electrified/rc2014-mystorm/hdl/src/rc2014_interface_top.v

`default_nettype none

module rc2014_interface_top(
    input [15:0] A,
    input [7:0] D,
    input RD,
    input M1,
    input CLK,
    input MRQ,
    input IORQ,
    input RST,
    input INT,
    input WR,
    output ADDR_DIR,
    output SIG_DIR,
    output DATA_DIR,
    output SIG2_DIR,
    output LED1,
    input BUT1,
    input fpga_clk,
    output uart_tx,
    input BUT2
    );

assign SIG_DIR = 0;
assign SIG2_DIR = 0;
assign DATA_DIR = 1;
assign ADDR_DIR = RD;

reg [31:0] led_countdown = 0;
wire led_track;
 
reg [7:0] request_counter =0;
reg ce = 0;

reg [7:0] romval;

rom blockram(.clk(CLK), 
  .ce(1),
  .addr(A[12:0]), 
  .rdata(romval));

reg debounced_CLK;

debouncer clockdebouncer(
  .CLK(fpga_clk),
  .raw_input(CLK),
  .state(debounced_CLK)
);

reg debounced_RD;

debouncer RDdebouncer(
  .CLK(fpga_clk),
  .raw_input(RD),
  .state(debounced_RD)
);

reg debounced_BUT1;

debouncer BUT1debouncer(
  .CLK(CLK),
  .raw_input(BUT1),
  .state(debounced_BUT1)
);


always @(posedge fpga_clk)
begin
	if (reset) begin
			text[0]  <= "0";
			text[1]  <= "x";
			text[2]  <= "_";
			text[3]  <= "_";
			text[4]  <= "_";
			text[5]  <= "_";
			text[6]  <= " ";
			text[7]  <= "0";
			text[8]  <= "x";
			text[9]  <= "_";
			text[10]  <= "_";
			text[11] <= "\n";
			text[12] <= 'h0d;
			
			text_cntr	<= 0;
			tx_req		<= 1'b0;

			asciidigits[0] <= "s";
			asciidigits[1] <= "c";
			asciidigits[2] <= "r";
			asciidigits[3] <= "w";

		end
		else if (text_cntr == 0) begin
			// asciidigits[0] <= "e";

			text[2]  <= asciidigits[3];
			text[3]  <= asciidigits[2];
			text[4]  <= asciidigits[1];
			text[5]  <= asciidigits[0];

			text[9]  <= asciidigits[5];
			text[10]  <= asciidigits[4];

			tx_req		<= 1'b0;

			if (count == 26'h50000) begin

				case (lastknownaddress[3:0])
					4'h0: asciidigits[0] <= "0";
					4'h1: asciidigits[0] <= "1";
					4'h2: asciidigits[0] <= "2";
					4'h3: asciidigits[0] <= "3";
					4'h4: asciidigits[0] <= "4";
					4'h5: asciidigits[0] <= "5";
					4'h6: asciidigits[0] <= "6";
					4'h7: asciidigits[0] <= "7";
					4'h8: asciidigits[0] <= "8";
					4'h9: asciidigits[0] <= "9";
					4'hA: asciidigits[0] <= "A";
					4'hB: asciidigits[0] <= "B";
					4'hC: asciidigits[0] <= "C";
					4'hD: asciidigits[0] <= "D";
					4'hE: asciidigits[0] <= "E";
					4'hF: asciidigits[0] <= "F";
					default: asciidigits[0] <= "Z";
				endcase

				case (lastknownaddress[7:4])
					4'h0: asciidigits[1] <= "0";
					4'h1: asciidigits[1] <= "1";
					4'h2: asciidigits[1] <= "2";
					4'h3: asciidigits[1] <= "3";
					4'h4: asciidigits[1] <= "4";
					4'h5: asciidigits[1] <= "5";
					4'h6: asciidigits[1] <= "6";
					4'h7: asciidigits[1] <= "7";
					4'h8: asciidigits[1] <= "8";
					4'h9: asciidigits[1] <= "9";
					4'hA: asciidigits[1] <= "A";
					4'hB: asciidigits[1] <= "B";
					4'hC: asciidigits[1] <= "C";
					4'hD: asciidigits[1] <= "D";
					4'hE: asciidigits[1] <= "E";
					4'hF: asciidigits[1] <= "F";
					default: asciidigits[1] <= "Z";
				endcase

				case (lastknownaddress[11:8])
					4'h0: asciidigits[2] <= "0";
					4'h1: asciidigits[2] <= "1";
					4'h2: asciidigits[2] <= "2";
					4'h3: asciidigits[2] <= "3";
					4'h4: asciidigits[2] <= "4";
					4'h5: asciidigits[2] <= "5";
					4'h6: asciidigits[2] <= "6";
					4'h7: asciidigits[2] <= "7";
					4'h8: asciidigits[2] <= "8";
					4'h9: asciidigits[2] <= "9";
					4'hA: asciidigits[2] <= "A";
					4'hB: asciidigits[2] <= "B";
					4'hC: asciidigits[2] <= "C";
					4'hD: asciidigits[2] <= "D";
					4'hE: asciidigits[2] <= "E";
					4'hF: asciidigits[2] <= "F";
					default: asciidigits[2] <= "Z";
				endcase

				case (lastknownaddress[15:12])
					4'h0: asciidigits[3] <= "0";
					4'h1: asciidigits[3] <= "1";
					4'h2: asciidigits[3] <= "2";
					4'h3: asciidigits[3] <= "3";
					4'h4: asciidigits[3] <= "4";
					4'h5: asciidigits[3] <= "5";
					4'h6: asciidigits[3] <= "6";
					4'h7: asciidigits[3] <= "7";
					4'h8: asciidigits[3] <= "8";
					4'h9: asciidigits[3] <= "9";
					4'hA: asciidigits[3] <= "A";
					4'hB: asciidigits[3] <= "B";
					4'hC: asciidigits[3] <= "C";
					4'hD: asciidigits[3] <= "D";
					4'hE: asciidigits[3] <= "E";
					4'hF: asciidigits[3] <= "F";
					default: asciidigits[3] <= "Z";
				endcase


				case (lastknownvalue[3:0])
					4'h0: asciidigits[4] <= "0";
					4'h1: asciidigits[4] <= "1";
					4'h2: asciidigits[4] <= "2";
					4'h3: asciidigits[4] <= "3";
					4'h4: asciidigits[4] <= "4";
					4'h5: asciidigits[4] <= "5";
					4'h6: asciidigits[4] <= "6";
					4'h7: asciidigits[4] <= "7";
					4'h8: asciidigits[4] <= "8";
					4'h9: asciidigits[4] <= "9";
					4'hA: asciidigits[4] <= "A";
					4'hB: asciidigits[4] <= "B";
					4'hC: asciidigits[4] <= "C";
					4'hD: asciidigits[4] <= "D";
					4'hE: asciidigits[4] <= "E";
					4'hF: asciidigits[4] <= "F";
					default: asciidigits[4] <= "Z";
				endcase

				case (lastknownvalue[7:4])
					4'h0: asciidigits[5] <= "0";
					4'h1: asciidigits[5] <= "1";
					4'h2: asciidigits[5] <= "2";
					4'h3: asciidigits[5] <= "3";
					4'h4: asciidigits[5] <= "4";
					4'h5: asciidigits[5] <= "5";
					4'h6: asciidigits[5] <= "6";
					4'h7: asciidigits[5] <= "7";
					4'h8: asciidigits[5] <= "8";
					4'h9: asciidigits[5] <= "9";
					4'hA: asciidigits[5] <= "A";
					4'hB: asciidigits[5] <= "B";
					4'hC: asciidigits[5] <= "C";
					4'hD: asciidigits[5] <= "D";
					4'hE: asciidigits[5] <= "E";
					4'hF: asciidigits[5] <= "F";
					default: asciidigits[5] <= "Z";
				endcase


				tx_req		<= 1'b1;
				tx_data		<= text[text_cntr];
				text_cntr	<= text_cntr + 1;
			end
		end
		else if (tx_ready) begin
			tx_req		<= 1'b1;
			tx_data		<= text[text_cntr];
			text_cntr	<= text_cntr + 1;

			if (text_cntr == 13) begin
				text_cntr	<= 0;
			end
			else begin
				text_cntr	<= text_cntr + 1;
			end
		end

    ce = (A >= 16'h0000 && A < 16'h2000) && !MRQ;
  // if (BUT1 == 1'b0)
  //    begin
        // led_countdown <= 0;
	      // // led_track <= 1'b0;
        led_track <= ~led_track;
    //  end
  end

  assign LED1 = led_track;

  reg [7:0] 	text[0:12];
  reg [16:0]	text_cntr;
  reg [15:0] lastknownaddress = 0;
  reg [7:0] lastknownvalue = 0;
  reg [7:0]	tx_data;
  reg 		tx_req;
  wire		tx_ready;
  wire reset;

  reg [26:0]	count;
  reg [7:0] asciidigits [0:5];
	
  sync_reset u_sync_reset(
		.clk(fpga_clk),
		.reset_in(BUT2),
		.reset_out(reset)
	);

	uart_tx u_uart_tx (
		.clk (fpga_clk),
		.reset (reset),
		.tx_req(tx_req),
		.tx_ready(tx_ready),
		.tx_data(tx_data),
		.uart_tx(uart_tx)
	);

endmodule
