electrified/rc2014-mystorm/hdl/chip.v

// Reading file 'chip.asc'..

module chip (output io_0_16_0, output io_0_16_1, input io_16_33_1, input io_0_27_1, output io_0_11_1, input io_0_28_0, output io_0_11_0, output io_0_18_1, output io_0_17_1, output io_0_17_0, input io_33_29_1, output io_0_20_0, output io_0_20_1, output io_0_18_0, input io_33_31_0, output io_0_22_0, output io_0_22_1, input io_0_27_0, input io_0_25_0, input io_3_33_1, input io_4_33_0, input io_33_30_1, input io_30_33_1, input io_31_33_0, input io_31_33_1, input io_30_33_0, input io_33_30_0, input io_33_27_1, input io_29_0_0, input io_33_23_1, input io_33_20_1, input io_33_21_1, input io_33_28_0, input io_33_21_0, output io_31_0_1);

wire n1;
// (0, 0, 'glb_netwk_0')
// (16, 1, 'sp4_r_v_b_36')
// (16, 2, 'sp4_r_v_b_25')
// (16, 3, 'sp4_r_v_b_12')
// (16, 4, 'sp4_r_v_b_1')
// (16, 5, 'sp4_r_v_b_36')
// (16, 6, 'sp4_r_v_b_25')
// (16, 7, 'sp4_r_v_b_12')
// (16, 8, 'sp4_r_v_b_1')
// (16, 9, 'sp4_r_v_b_36')
// (16, 10, 'neigh_op_tnr_6')
// (16, 10, 'sp4_r_v_b_25')
// (16, 11, 'lutff_global/s_r')
// (16, 11, 'neigh_op_rgt_6')
// (16, 11, 'sp4_r_v_b_12')
// (16, 12, 'lutff_global/s_r')
// (16, 12, 'neigh_op_bnr_6')
// (16, 12, 'sp4_r_v_b_1')
// (17, 0, 'fabout')
// (17, 0, 'local_g1_4')
// (17, 0, 'span4_vert_36')
// (17, 1, 'sp4_v_b_36')
// (17, 2, 'sp4_v_b_25')
// (17, 3, 'sp4_v_b_12')
// (17, 4, 'sp4_v_b_1')
// (17, 4, 'sp4_v_t_36')
// (17, 5, 'sp4_v_b_36')
// (17, 6, 'sp4_v_b_25')
// (17, 7, 'sp4_v_b_12')
// (17, 8, 'sp4_v_b_1')
// (17, 8, 'sp4_v_t_36')
// (17, 9, 'sp4_v_b_36')
// (17, 10, 'neigh_op_top_6')
// (17, 10, 'sp4_v_b_25')
// (17, 11, 'lutff_6/out')
// (17, 11, 'lutff_global/s_r')
// (17, 11, 'sp4_v_b_12')
// (17, 12, 'local_g1_6')
// (17, 12, 'lutff_3/in_2')
// (17, 12, 'neigh_op_bot_6')
// (17, 12, 'sp4_v_b_1')
// (18, 10, 'local_g2_6')
// (18, 10, 'lutff_7/in_1')
// (18, 10, 'lutff_global/s_r')
// (18, 10, 'neigh_op_tnl_6')
// (18, 11, 'neigh_op_lft_6')
// (18, 12, 'neigh_op_bnl_6')

wire io_0_16_0;
assign io_0_16_1 = io_0_16_0;
// (0, 0, 'glb_netwk_3')
// (0, 16, 'io_0/D_OUT_0')
// (0, 16, 'io_0/PAD')
// (0, 16, 'io_1/D_OUT_0')
// (0, 16, 'io_1/PAD')
// (0, 16, 'local_g0_7')
// (0, 16, 'local_g1_7')
// (0, 16, 'span4_horz_7')
// (0, 16, 'span4_vert_t_13')
// (0, 17, 'fabout')
// (0, 17, 'local_g0_5')
// (0, 17, 'span4_vert_b_13')
// (0, 18, 'span4_vert_b_9')
// (0, 19, 'span4_vert_b_5')
// (0, 20, 'span4_horz_7')
// (0, 20, 'span4_vert_b_1')
// (1, 16, 'sp4_h_r_18')
// (1, 20, 'sp4_h_r_18')
// (2, 16, 'sp4_h_r_31')
// (2, 20, 'sp4_h_r_31')
// (3, 16, 'sp4_h_r_42')
// (3, 20, 'sp4_h_r_42')
// (4, 16, 'sp4_h_l_42')
// (4, 16, 'sp4_h_r_11')
// (4, 20, 'sp4_h_l_42')
// (4, 20, 'sp4_h_r_11')
// (5, 16, 'sp4_h_r_22')
// (5, 20, 'sp4_h_r_22')
// (6, 16, 'sp4_h_r_35')
// (6, 20, 'sp4_h_r_35')
// (7, 16, 'sp4_h_r_46')
// (7, 20, 'sp4_h_r_46')
// (7, 24, 'sp4_r_v_b_43')
// (7, 25, 'sp4_r_v_b_30')
// (7, 25, 'sp4_r_v_b_46')
// (7, 26, 'sp4_r_v_b_19')
// (7, 26, 'sp4_r_v_b_35')
// (7, 27, 'sp4_r_v_b_22')
// (7, 27, 'sp4_r_v_b_6')
// (7, 28, 'sp4_r_v_b_11')
// (8, 11, 'sp12_v_t_23')
// (8, 12, 'sp12_v_b_23')
// (8, 13, 'sp12_v_b_20')
// (8, 14, 'sp12_v_b_19')
// (8, 15, 'sp12_v_b_16')
// (8, 16, 'local_g1_3')
// (8, 16, 'ram/WCLK')
// (8, 16, 'ram/WCLKE')
// (8, 16, 'sp12_v_b_15')
// (8, 16, 'sp4_h_l_46')
// (8, 16, 'sp4_h_r_11')
// (8, 16, 'sp4_r_v_b_43')
// (8, 17, 'sp12_v_b_12')
// (8, 17, 'sp4_r_v_b_30')
// (8, 18, 'local_g3_3')
// (8, 18, 'ram/WCLK')
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
// (26, 26, 'sp4_v_b_19')
// (26, 27, 'sp4_v_b_3')
// (26, 27, 'sp4_v_b_6')
// (26, 27, 'sp4_v_t_43')
// (26, 28, 'sp4_v_b_43')
// (26, 29, 'sp4_v_b_30')
// (26, 30, 'sp4_v_b_19')
// (26, 31, 'sp4_v_b_6')
// (27, 20, 'sp4_h_r_35')
// (27, 23, 'sp4_h_r_19')
// (27, 24, 'sp4_h_r_34')
// (28, 20, 'sp4_h_r_46')
// (28, 23, 'sp4_h_r_30')
// (28, 24, 'sp4_h_r_47')
// (29, 20, 'sp4_h_l_46')
// (29, 23, 'sp4_h_r_43')
// (29, 24, 'sp4_h_l_47')
// (30, 23, 'sp4_h_l_43')

wire io_16_33_1;
// (0, 0, 'glb_netwk_4')
// (15, 15, 'lutff_global/clk')
// (15, 32, 'neigh_op_tnr_2')
// (15, 32, 'neigh_op_tnr_6')
// (16, 13, 'lutff_global/clk')
// (16, 14, 'lutff_global/clk')
// (16, 15, 'lutff_global/clk')
// (16, 32, 'neigh_op_top_2')
// (16, 32, 'neigh_op_top_6')
// (16, 33, 'fabout')
// (16, 33, 'io_1/D_IN_0')
// (16, 33, 'io_1/PAD')
// (16, 33, 'local_g1_2')
// (16, 33, 'span4_horz_r_2')
// (17, 32, 'neigh_op_tnl_2')
// (17, 32, 'neigh_op_tnl_6')
// (17, 33, 'span4_horz_r_6')
// (18, 33, 'span4_horz_r_10')
// (19, 33, 'span4_horz_r_14')
// (20, 33, 'span4_horz_l_14')

reg n4 = 0;
// (0, 0, 'glb_netwk_5')
// (6, 20, 'lutff_global/clk')
// (6, 21, 'lutff_global/clk')
// (7, 19, 'lutff_global/clk')
// (7, 20, 'lutff_global/clk')
// (7, 21, 'lutff_global/clk')
// (7, 22, 'lutff_global/clk')
// (15, 1, 'sp4_r_v_b_9')
// (15, 2, 'sp4_r_v_b_43')
// (15, 3, 'sp4_r_v_b_30')
// (15, 4, 'sp4_r_v_b_19')
// (15, 5, 'sp4_r_v_b_6')
// (15, 6, 'sp4_r_v_b_47')
// (15, 7, 'sp4_r_v_b_34')
// (15, 8, 'sp4_r_v_b_23')
// (15, 9, 'sp4_r_v_b_10')
// (15, 10, 'sp4_r_v_b_47')
// (15, 11, 'sp4_r_v_b_34')
// (15, 12, 'neigh_op_tnr_5')
// (15, 12, 'sp4_r_v_b_23')
// (15, 13, 'neigh_op_rgt_5')
// (15, 13, 'sp4_r_v_b_10')
// (15, 14, 'neigh_op_bnr_5')
// (16, 0, 'fabout')
// (16, 0, 'local_g0_1')
// (16, 0, 'span4_vert_9')
// (16, 1, 'sp4_v_b_9')
// (16, 1, 'sp4_v_t_43')
// (16, 2, 'sp4_v_b_43')
// (16, 3, 'sp4_v_b_30')
// (16, 4, 'sp4_v_b_19')
// (16, 5, 'sp4_v_b_6')
// (16, 5, 'sp4_v_t_47')
// (16, 6, 'sp4_v_b_47')
// (16, 7, 'sp4_v_b_34')
// (16, 8, 'sp4_v_b_23')
// (16, 9, 'sp4_v_b_10')
// (16, 9, 'sp4_v_t_47')
// (16, 10, 'sp4_v_b_47')
// (16, 11, 'lutff_global/clk')
// (16, 11, 'sp4_v_b_34')
// (16, 12, 'lutff_global/clk')
// (16, 12, 'neigh_op_top_5')
// (16, 12, 'sp4_v_b_23')
// (16, 13, 'local_g0_5')
// (16, 13, 'lutff_5/in_0')
// (16, 13, 'lutff_5/out')
// (16, 13, 'sp4_v_b_10')
// (16, 14, 'local_g1_5')
// (16, 14, 'lutff_4/in_0')
// (16, 14, 'neigh_op_bot_5')
// (17, 11, 'lutff_global/clk')
// (17, 12, 'neigh_op_tnl_5')
// (17, 13, 'neigh_op_lft_5')
// (17, 14, 'neigh_op_bnl_5')
// (18, 10, 'lutff_global/clk')

wire io_0_27_1;
// (0, 0, 'glb_netwk_6')
// (0, 15, 'span4_vert_t_14')
// (0, 16, 'fabout')
// (0, 16, 'local_g1_6')
// (0, 16, 'span4_vert_b_14')
// (0, 17, 'span4_vert_b_10')
// (0, 18, 'span4_vert_b_6')
// (0, 19, 'span4_vert_b_2')
// (0, 19, 'span4_vert_t_14')
// (0, 20, 'span4_vert_b_14')
// (0, 21, 'span4_vert_b_10')
// (0, 22, 'span4_vert_b_6')
// (0, 23, 'span4_vert_b_2')
// (0, 23, 'span4_vert_t_14')
// (0, 24, 'span4_vert_b_14')
// (0, 25, 'span4_vert_b_10')
// (0, 26, 'span4_vert_b_6')
// (0, 27, 'io_1/D_IN_0')
// (0, 27, 'io_1/PAD')
// (0, 27, 'span12_horz_4')
// (0, 27, 'span4_vert_b_2')
// (1, 26, 'neigh_op_tnl_2')
// (1, 26, 'neigh_op_tnl_6')
// (1, 27, 'neigh_op_lft_2')
// (1, 27, 'neigh_op_lft_6')
// (1, 27, 'sp12_h_r_7')
// (1, 28, 'neigh_op_bnl_2')
// (1, 28, 'neigh_op_bnl_6')
// (2, 27, 'sp12_h_r_8')
// (3, 27, 'sp12_h_r_11')
// (4, 27, 'sp12_h_r_12')
// (5, 27, 'sp12_h_r_15')
// (6, 27, 'sp12_h_r_16')
// (7, 27, 'sp12_h_r_19')
// (8, 15, 'ram/RCLK')
// (8, 17, 'ram/RCLK')
// (8, 19, 'ram/RCLK')
// (8, 21, 'ram/RCLK')
// (8, 23, 'ram/RCLK')
// (8, 25, 'ram/RCLK')
// (8, 27, 'ram/RCLK')
// (8, 27, 'sp12_h_r_20')
// (8, 29, 'ram/RCLK')
// (9, 16, 'sp4_r_v_b_45')
// (9, 17, 'sp4_r_v_b_32')
// (9, 18, 'sp4_r_v_b_21')
// (9, 19, 'sp4_r_v_b_8')
// (9, 27, 'sp12_h_r_23')
// (10, 15, 'sp12_v_t_23')
// (10, 15, 'sp4_h_r_8')
// (10, 15, 'sp4_v_t_45')
// (10, 16, 'sp12_v_b_23')
// (10, 16, 'sp4_v_b_45')
// (10, 17, 'sp12_v_b_20')
// (10, 17, 'sp4_v_b_32')
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
// (7, 18, 'neigh_op_top_0')
// (7, 19, 'lutff_0/out')
// (7, 19, 'sp4_h_r_16')
// (7, 20, 'neigh_op_bot_0')
// (8, 18, 'neigh_op_tnl_0')
// (8, 19, 'neigh_op_lft_0')
// (8, 19, 'sp4_h_r_29')
// (8, 20, 'neigh_op_bnl_0')
// (9, 19, 'sp4_h_r_40')
// (10, 19, 'sp4_h_l_40')

reg io_0_17_1 = 0;
// (0, 15, 'span4_vert_t_13')
// (0, 16, 'span4_vert_b_13')
// (0, 17, 'io_1/D_OUT_0')
// (0, 17, 'io_1/PAD')
// (0, 17, 'local_g0_1')
// (0, 17, 'span4_vert_b_9')
// (0, 18, 'span4_vert_b_5')
// (0, 19, 'span4_horz_31')
// (0, 19, 'span4_vert_b_1')
// (1, 19, 'sp4_h_r_42')
// (2, 19, 'sp4_h_l_42')
// (2, 19, 'sp4_h_r_7')
// (3, 19, 'sp4_h_r_18')
// (4, 19, 'sp4_h_r_31')
// (5, 19, 'sp4_h_r_42')
// (6, 18, 'neigh_op_tnr_3')
// (6, 19, 'neigh_op_rgt_3')
// (6, 19, 'sp4_h_l_42')
// (6, 19, 'sp4_h_r_11')
// (6, 20, 'neigh_op_bnr_3')
// (7, 18, 'neigh_op_top_3')
// (7, 19, 'lutff_3/out')
// (7, 19, 'sp4_h_r_22')
// (7, 20, 'neigh_op_bot_3')
// (8, 18, 'neigh_op_tnl_3')
// (8, 19, 'neigh_op_lft_3')
// (8, 19, 'sp4_h_r_35')
// (8, 20, 'neigh_op_bnl_3')
// (9, 19, 'sp4_h_r_46')
// (10, 19, 'sp4_h_l_46')

reg io_0_17_0 = 0;
// (0, 17, 'io_0/D_OUT_0')
// (0, 17, 'io_0/PAD')
// (0, 17, 'local_g0_2')
// (0, 17, 'span4_horz_18')
// (1, 17, 'sp4_h_r_31')
// (2, 17, 'sp4_h_r_42')
// (3, 17, 'sp4_h_l_42')
// (3, 17, 'sp4_h_r_4')
// (4, 17, 'sp4_h_r_17')
// (5, 17, 'sp4_h_r_28')
// (6, 17, 'sp4_h_r_41')
// (6, 18, 'sp4_r_v_b_47')
// (6, 19, 'sp4_r_v_b_34')
// (6, 20, 'neigh_op_tnr_5')
// (6, 20, 'sp4_r_v_b_23')
// (6, 21, 'neigh_op_rgt_5')
// (6, 21, 'sp4_r_v_b_10')
// (6, 22, 'neigh_op_bnr_5')
// (7, 17, 'sp4_h_l_41')
// (7, 17, 'sp4_v_t_47')
// (7, 18, 'sp4_v_b_47')
// (7, 19, 'sp4_v_b_34')
// (7, 20, 'neigh_op_top_5')
// (7, 20, 'sp4_v_b_23')
// (7, 21, 'lutff_5/out')
// (7, 21, 'sp4_v_b_10')
// (7, 22, 'neigh_op_bot_5')
// (8, 20, 'neigh_op_tnl_5')
// (8, 21, 'neigh_op_lft_5')
// (8, 22, 'neigh_op_bnl_5')

wire io_33_29_1;
// (0, 17, 'span12_horz_4')
// (1, 17, 'sp12_h_r_7')
// (2, 17, 'sp12_h_r_8')
// (3, 17, 'sp12_h_r_11')
// (4, 17, 'sp12_h_r_12')
// (5, 17, 'sp12_h_r_15')
// (6, 15, 'sp4_h_r_4')
// (6, 17, 'sp12_h_r_16')
// (6, 19, 'sp4_h_r_3')
// (6, 21, 'sp4_h_r_4')
// (7, 15, 'sp4_h_r_17')
// (7, 17, 'sp12_h_r_19')
// (7, 19, 'sp4_h_r_14')
// (7, 21, 'sp4_h_r_17')
// (7, 29, 'sp4_h_r_6')
// (8, 15, 'local_g3_4')
// (8, 15, 'ram/RADDR_8')
// (8, 15, 'sp4_h_r_28')
// (8, 17, 'local_g1_4')
// (8, 17, 'ram/RADDR_8')
// (8, 17, 'sp12_h_r_20')
// (8, 19, 'local_g2_3')
// (8, 19, 'ram/RADDR_8')
// (8, 19, 'sp4_h_r_27')
// (8, 21, 'local_g3_4')
// (8, 21, 'ram/RADDR_8')
// (8, 21, 'sp4_h_r_28')
// (8, 22, 'sp4_r_v_b_39')
// (8, 23, 'local_g1_2')
// (8, 23, 'ram/RADDR_8')
// (8, 23, 'sp4_r_v_b_26')
// (8, 24, 'sp4_r_v_b_15')
// (8, 25, 'local_g1_2')
// (8, 25, 'ram/RADDR_8')
// (8, 25, 'sp4_r_v_b_2')
// (8, 26, 'sp4_r_v_b_36')
// (8, 26, 'sp4_r_v_b_43')
// (8, 27, 'local_g0_1')
// (8, 27, 'ram/RADDR_8')
// (8, 27, 'sp4_r_v_b_25')
// (8, 27, 'sp4_r_v_b_30')
// (8, 28, 'sp4_r_v_b_12')
// (8, 28, 'sp4_r_v_b_19')
// (8, 29, 'local_g0_3')
// (8, 29, 'ram/RADDR_8')
// (8, 29, 'sp4_h_r_19')
// (8, 29, 'sp4_r_v_b_1')
// (8, 29, 'sp4_r_v_b_6')
// (9, 15, 'sp4_h_r_41')
// (9, 16, 'sp4_r_v_b_47')
// (9, 17, 'sp12_h_r_23')
// (9, 17, 'sp4_r_v_b_34')
// (9, 18, 'sp4_r_v_b_23')
// (9, 19, 'sp4_h_r_38')
// (9, 19, 'sp4_r_v_b_10')
// (9, 21, 'sp4_h_r_41')
// (9, 21, 'sp4_v_t_39')
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
// (6, 21, 'sp4_h_r_29')
// (6, 22, 'neigh_op_bnr_4')
// (7, 20, 'neigh_op_top_4')
// (7, 21, 'lutff_4/out')
// (7, 21, 'sp4_h_r_40')
// (7, 22, 'neigh_op_bot_4')
// (8, 20, 'neigh_op_tnl_4')
// (8, 21, 'neigh_op_lft_4')
// (8, 21, 'sp4_h_l_40')
// (8, 22, 'neigh_op_bnl_4')

reg io_0_20_1 = 0;
// (0, 17, 'span4_vert_t_15')
// (0, 18, 'span4_vert_b_15')
// (0, 19, 'span4_vert_b_11')
// (0, 20, 'io_1/D_OUT_0')
// (0, 20, 'io_1/PAD')
// (0, 20, 'local_g0_7')
// (0, 20, 'span4_vert_b_7')
// (0, 21, 'span4_horz_43')
// (0, 21, 'span4_vert_b_3')
// (1, 21, 'sp4_h_l_43')
// (1, 21, 'sp4_h_r_10')
// (2, 21, 'sp4_h_r_23')
// (3, 21, 'sp4_h_r_34')
// (4, 21, 'sp4_h_r_47')
// (5, 21, 'sp4_h_l_47')
// (5, 21, 'sp4_h_r_10')
// (6, 20, 'neigh_op_tnr_1')
// (6, 21, 'neigh_op_rgt_1')
// (6, 21, 'sp4_h_r_23')
// (6, 22, 'neigh_op_bnr_1')
// (7, 20, 'neigh_op_top_1')
// (7, 21, 'lutff_1/out')
// (7, 21, 'sp4_h_r_34')
// (7, 22, 'neigh_op_bot_1')
// (8, 20, 'neigh_op_tnl_1')
// (8, 21, 'neigh_op_lft_1')
// (8, 21, 'sp4_h_r_47')
// (8, 22, 'neigh_op_bnl_1')
// (9, 21, 'sp4_h_l_47')

reg io_0_18_0 = 0;
// (0, 18, 'io_0/D_OUT_0')
// (0, 18, 'io_0/PAD')
// (0, 18, 'local_g1_3')
// (0, 18, 'span4_horz_19')
// (1, 18, 'sp4_h_r_30')
// (2, 18, 'sp4_h_r_43')
// (3, 18, 'sp4_h_l_43')
// (3, 18, 'sp4_h_r_3')
// (4, 18, 'sp4_h_r_14')
// (5, 18, 'sp4_h_r_27')
// (6, 18, 'sp4_h_r_38')
// (6, 19, 'sp4_r_v_b_38')
// (6, 20, 'neigh_op_tnr_7')
// (6, 20, 'sp4_r_v_b_27')
// (6, 21, 'neigh_op_rgt_7')
// (6, 21, 'sp4_r_v_b_14')
// (6, 22, 'neigh_op_bnr_7')
// (6, 22, 'sp4_r_v_b_3')
// (7, 18, 'sp4_h_l_38')
// (7, 18, 'sp4_v_t_38')
// (7, 19, 'sp4_v_b_38')
// (7, 20, 'neigh_op_top_7')
// (7, 20, 'sp4_v_b_27')
// (7, 21, 'lutff_7/out')
// (7, 21, 'sp4_v_b_14')
// (7, 22, 'neigh_op_bot_7')
// (7, 22, 'sp4_v_b_3')
// (8, 20, 'neigh_op_tnl_7')
// (8, 21, 'neigh_op_lft_7')
// (8, 22, 'neigh_op_bnl_7')

wire io_33_31_0;
// (0, 19, 'span12_horz_0')
// (1, 19, 'sp12_h_r_3')
// (2, 19, 'sp12_h_r_4')
// (3, 19, 'sp12_h_r_7')
// (4, 19, 'sp12_h_r_8')
// (5, 19, 'sp12_h_r_11')
// (6, 19, 'sp12_h_r_12')
// (7, 19, 'sp12_h_r_15')
// (8, 15, 'local_g1_1')
// (8, 15, 'ram/RADDR_7')
// (8, 15, 'sp4_h_r_9')
// (8, 17, 'local_g0_2')
// (8, 17, 'ram/RADDR_7')
// (8, 17, 'sp4_h_r_10')
// (8, 19, 'local_g0_0')
// (8, 19, 'ram/RADDR_7')
// (8, 19, 'sp12_h_r_16')
// (8, 21, 'local_g0_2')
// (8, 21, 'ram/RADDR_7')
// (8, 21, 'sp4_h_r_10')
// (8, 23, 'local_g1_1')
// (8, 23, 'ram/RADDR_7')
// (8, 23, 'sp4_h_r_1')
// (8, 25, 'local_g0_6')
// (8, 25, 'ram/RADDR_7')
// (8, 25, 'sp4_h_r_6')
// (8, 27, 'local_g1_1')
// (8, 27, 'ram/RADDR_7')
// (8, 27, 'sp4_h_r_9')
// (8, 29, 'local_g0_2')
// (8, 29, 'ram/RADDR_7')
// (8, 29, 'sp4_h_r_2')
// (9, 15, 'sp4_h_r_20')
// (9, 17, 'sp4_h_r_23')
// (9, 19, 'sp12_h_r_19')
// (9, 21, 'sp4_h_r_23')
// (9, 23, 'sp4_h_r_12')
// (9, 25, 'sp4_h_r_19')
// (9, 27, 'sp4_h_r_20')
// (9, 29, 'sp4_h_r_15')
// (10, 15, 'sp4_h_r_33')
// (10, 17, 'sp4_h_r_34')
// (10, 19, 'sp12_h_r_20')
// (10, 21, 'sp4_h_r_34')
// (10, 23, 'sp4_h_r_25')
// (10, 25, 'sp4_h_r_30')
// (10, 27, 'sp4_h_r_33')
// (10, 29, 'sp4_h_r_26')
// (11, 12, 'sp4_r_v_b_41')
// (11, 13, 'sp4_r_v_b_28')
// (11, 14, 'sp4_r_v_b_17')
// (11, 15, 'sp4_h_r_44')
// (11, 15, 'sp4_r_v_b_4')
// (11, 17, 'sp4_h_r_47')
// (11, 18, 'sp4_r_v_b_47')
// (11, 19, 'sp12_h_r_23')
// (11, 19, 'sp4_r_v_b_34')
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
// (33, 19, 'span12_horz_16')
// (33, 23, 'span4_horz_1')
// (33, 23, 'span4_vert_t_12')
// (33, 24, 'span4_vert_b_12')
// (33, 25, 'span4_vert_b_8')
// (33, 26, 'span4_vert_b_4')
// (33, 27, 'span4_horz_25')
// (33, 27, 'span4_vert_b_0')
// (33, 27, 'span4_vert_t_12')
// (33, 28, 'span4_vert_b_12')
// (33, 29, 'span4_vert_b_8')
// (33, 30, 'span4_vert_b_4')
// (33, 31, 'io_0/D_IN_0')
// (33, 31, 'io_0/PAD')
// (33, 31, 'span12_horz_16')
// (33, 31, 'span4_horz_40')
// (33, 31, 'span4_vert_b_0')

reg io_0_22_0 = 0;
// (0, 22, 'io_0/D_OUT_0')
// (0, 22, 'io_0/PAD')
// (0, 22, 'local_g1_5')
// (0, 22, 'span12_horz_5')
// (1, 22, 'sp12_h_r_6')
// (2, 22, 'sp12_h_r_9')
// (3, 22, 'sp12_h_r_10')
// (4, 22, 'sp12_h_r_13')
// (5, 22, 'sp12_h_r_14')
// (6, 21, 'neigh_op_tnr_5')
// (6, 22, 'neigh_op_rgt_5')
// (6, 22, 'sp12_h_r_17')
// (6, 23, 'neigh_op_bnr_5')
// (7, 21, 'neigh_op_top_5')
// (7, 22, 'lutff_5/out')
// (7, 22, 'sp12_h_r_18')
// (7, 23, 'neigh_op_bot_5')
// (8, 21, 'neigh_op_tnl_5')
// (8, 22, 'neigh_op_lft_5')
// (8, 22, 'sp12_h_r_21')
// (8, 23, 'neigh_op_bnl_5')
// (9, 22, 'sp12_h_r_22')
// (10, 22, 'sp12_h_l_22')

reg io_0_22_1 = 0;
// (0, 22, 'io_1/D_OUT_0')
// (0, 22, 'io_1/PAD')
// (0, 22, 'local_g0_1')
// (0, 22, 'span4_horz_41')
// (1, 22, 'sp4_h_l_41')
// (1, 22, 'sp4_h_r_1')
// (2, 22, 'sp4_h_r_12')
// (3, 22, 'sp4_h_r_25')
// (4, 22, 'sp4_h_r_36')
// (5, 22, 'sp4_h_l_36')
// (5, 22, 'sp4_h_r_10')
// (6, 21, 'neigh_op_tnr_1')
// (6, 22, 'neigh_op_rgt_1')
// (6, 22, 'sp4_h_r_23')
// (6, 23, 'neigh_op_bnr_1')
// (7, 21, 'neigh_op_top_1')
// (7, 22, 'lutff_1/out')
// (7, 22, 'sp4_h_r_34')
// (7, 23, 'neigh_op_bot_1')
// (8, 21, 'neigh_op_tnl_1')
// (8, 22, 'neigh_op_lft_1')
// (8, 22, 'sp4_h_r_47')
// (8, 23, 'neigh_op_bnl_1')
// (9, 22, 'sp4_h_l_47')

wire n18;
// (0, 22, 'logic_op_tnr_0')
// (0, 23, 'logic_op_rgt_0')
// (0, 23, 'span4_horz_5')
// (0, 24, 'logic_op_bnr_0')
// (1, 20, 'sp4_r_v_b_36')
// (1, 21, 'sp4_r_v_b_25')
// (1, 21, 'sp4_r_v_b_41')
// (1, 22, 'neigh_op_top_0')
// (1, 22, 'sp4_r_v_b_12')
// (1, 22, 'sp4_r_v_b_28')
// (1, 22, 'sp4_r_v_b_44')
// (1, 23, 'lutff_0/out')
// (1, 23, 'sp4_h_r_16')
// (1, 23, 'sp4_r_v_b_1')
// (1, 23, 'sp4_r_v_b_17')
// (1, 23, 'sp4_r_v_b_33')
// (1, 24, 'neigh_op_bot_0')
// (1, 24, 'sp4_r_v_b_20')
// (1, 24, 'sp4_r_v_b_4')
// (1, 25, 'sp4_r_v_b_9')
// (2, 19, 'sp4_h_r_1')
// (2, 19, 'sp4_v_t_36')
// (2, 20, 'sp4_h_r_4')
// (2, 20, 'sp4_v_b_36')
// (2, 20, 'sp4_v_t_41')
// (2, 21, 'sp4_h_r_9')
// (2, 21, 'sp4_v_b_25')
// (2, 21, 'sp4_v_b_41')
// (2, 21, 'sp4_v_t_44')
// (2, 22, 'neigh_op_tnl_0')
// (2, 22, 'sp4_v_b_12')
// (2, 22, 'sp4_v_b_28')
// (2, 22, 'sp4_v_b_44')
// (2, 23, 'neigh_op_lft_0')
// (2, 23, 'sp4_h_r_29')
// (2, 23, 'sp4_v_b_1')
// (2, 23, 'sp4_v_b_17')
// (2, 23, 'sp4_v_b_33')
// (2, 24, 'neigh_op_bnl_0')
// (2, 24, 'sp4_v_b_20')
// (2, 24, 'sp4_v_b_4')
// (2, 25, 'sp4_v_b_9')
// (3, 19, 'sp4_h_r_12')
// (3, 20, 'sp4_h_r_17')
// (3, 21, 'sp4_h_r_20')
// (3, 23, 'sp4_h_r_40')
// (4, 19, 'sp4_h_r_25')
// (4, 20, 'sp4_h_r_28')
// (4, 21, 'sp4_h_r_33')
// (4, 23, 'sp4_h_l_40')
// (4, 23, 'sp4_h_r_8')
// (5, 17, 'sp4_r_v_b_47')
// (5, 18, 'sp4_r_v_b_34')
// (5, 19, 'sp4_h_r_36')
// (5, 19, 'sp4_r_v_b_23')
// (5, 20, 'sp4_h_r_41')
// (5, 20, 'sp4_r_v_b_10')
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
// (31, 21, 'sp12_h_l_23')
// (31, 21, 'sp12_v_t_23')
// (31, 21, 'sp4_v_b_34')
// (31, 21, 'sp4_v_b_4')
// (31, 21, 'sp4_v_t_45')
// (31, 22, 'sp12_v_b_23')
// (31, 22, 'sp4_v_b_23')
// (31, 22, 'sp4_v_b_45')
// (31, 23, 'sp12_v_b_20')
// (31, 23, 'sp4_h_l_38')
// (31, 23, 'sp4_v_b_10')
// (31, 23, 'sp4_v_b_32')
// (31, 24, 'sp12_v_b_19')
// (31, 24, 'sp4_v_b_21')
// (31, 25, 'sp12_v_b_16')
// (31, 25, 'sp4_v_b_8')
// (31, 26, 'sp12_v_b_15')
// (31, 27, 'sp12_v_b_12')
// (31, 28, 'sp12_v_b_11')
// (31, 29, 'sp12_v_b_8')
// (31, 30, 'sp12_v_b_7')
// (31, 31, 'sp12_v_b_4')
// (31, 32, 'neigh_op_top_0')
// (31, 32, 'neigh_op_top_4')
// (31, 32, 'sp12_v_b_3')
// (31, 33, 'io_0/D_IN_0')
// (31, 33, 'io_0/PAD')
// (31, 33, 'span12_vert_0')
// (31, 33, 'span4_horz_r_12')
// (32, 32, 'neigh_op_tnl_0')
// (32, 32, 'neigh_op_tnl_4')
// (32, 33, 'span4_horz_l_12')
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
