electrified/rc2014-mystorm/hdl/src/debouncer.v

`default_nettype none

module debouncer(
    input CLK,
    input raw_input,
    output reg state,
    // output trans_up,
    // output trans_dn
    );

// Synchronize the switch input to the clock
reg sync_0, sync_1;
always @(posedge CLK) 
begin
  sync_0 = raw_input;
end
	
always @(posedge CLK) 
begin
  sync_1 = sync_0;
end

// Debounce the switch
reg [2:0] count;
wire idle = (state == sync_1);
wire finished = &count;	// true when all bits of count are 1's

always @(posedge CLK)
begin
  if (idle)
  begin
    count <= 0;
  end
  else 
  begin
    count <= count + 2'd1;  
    if (finished)
    begin
      state <= ~state;  
    end
  end
end

// assign trans_dn = ~idle & finished & ~state;
// assign trans_up = ~idle & finished & state;

endmodule
